Ivan-Lopez/Mano-Robotica/Images/others/dedoV2.jpg

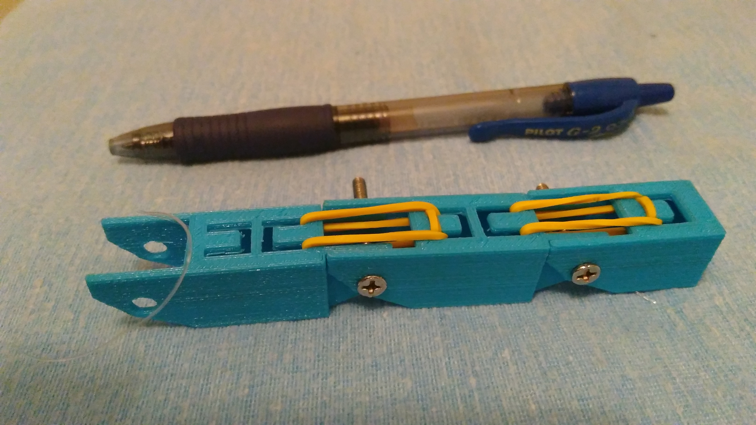
Images/others/dedoV2.jpg
