Ivan-Lopez/Mano-Robotica/Images/others/IMG_20180927_234917.jpg

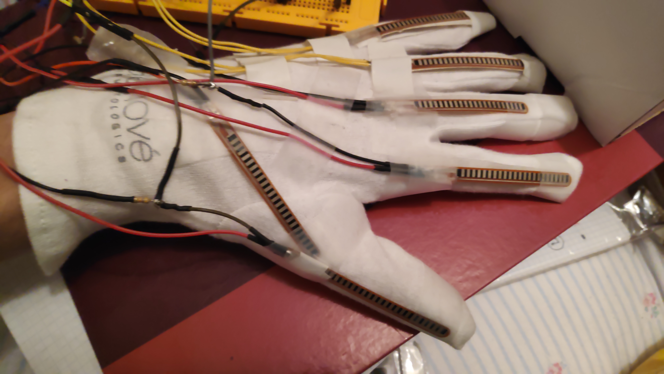
Images/others/IMG_20180927_234917.jpg
