Ivan-Lopez/Mano-Robotica/Images/plans/Falange distal meñique.jpg

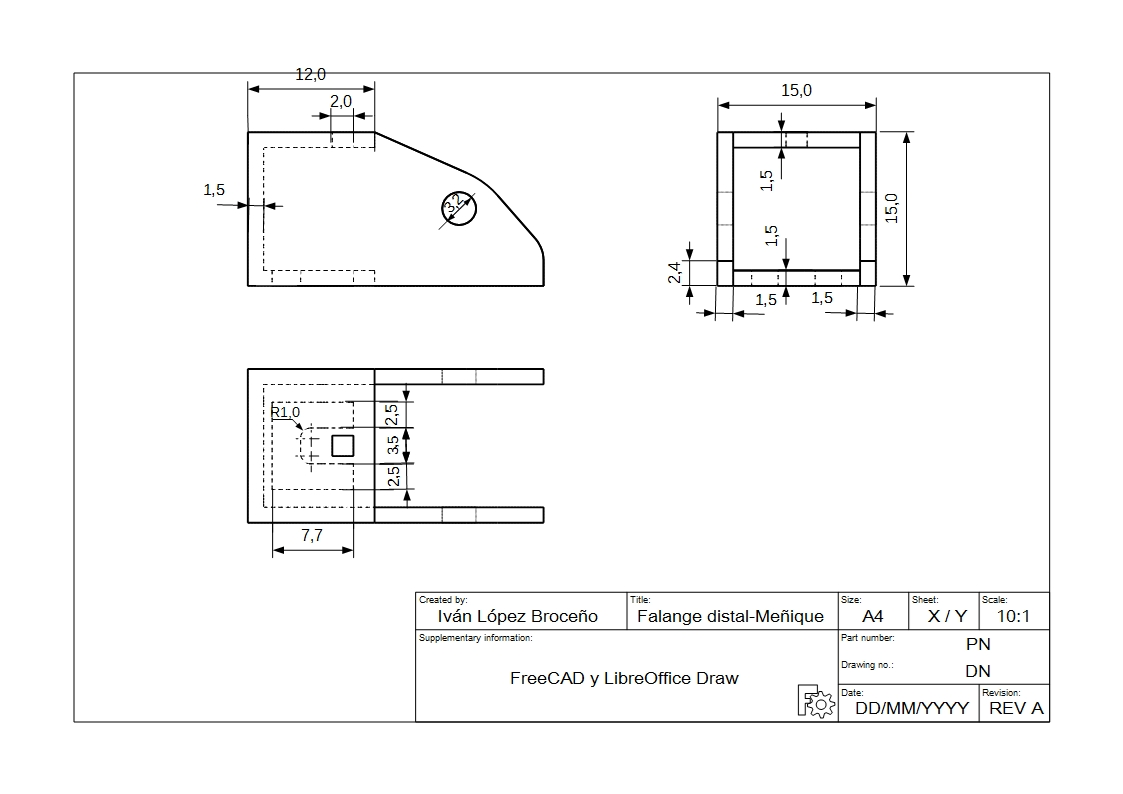
Images/plans/Falange distal meñique.jpg
