Ivan-Lopez/Mano-Robotica/Images/plans/falange distal pulgar.jpg

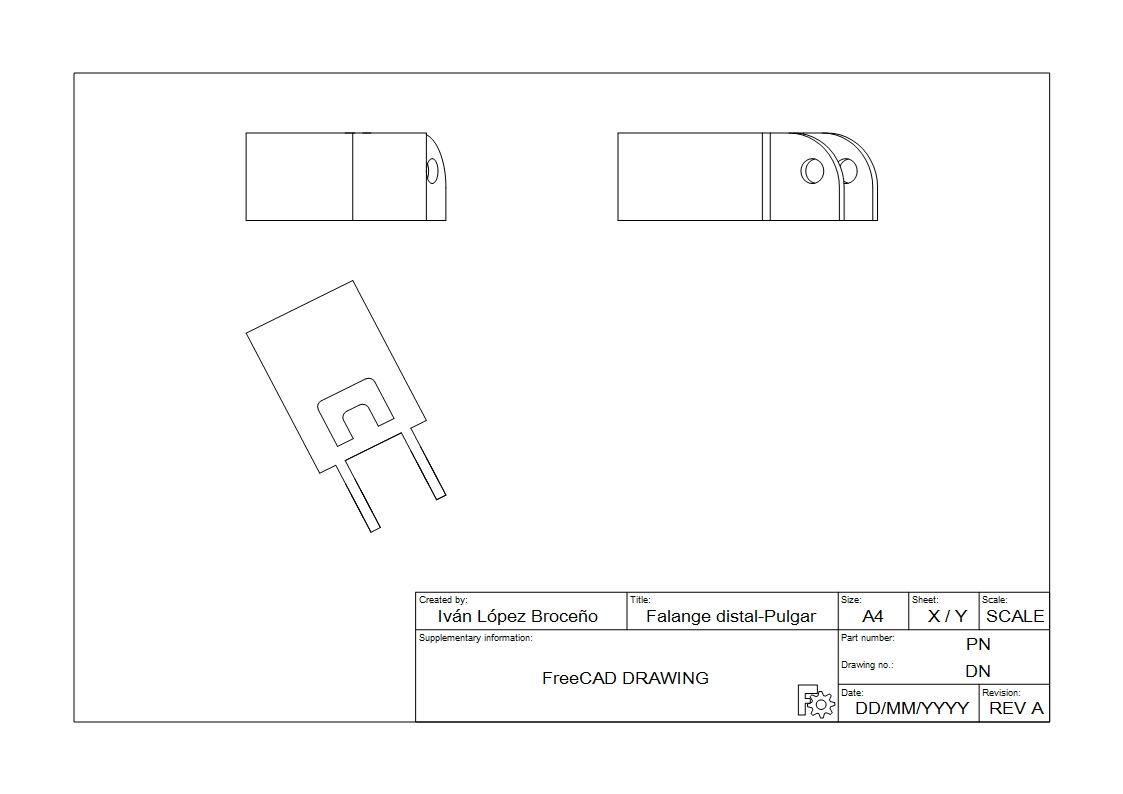
Images/plans/falange distal pulgar.jpg
