Ivan-Lopez/Mano-Robotica/Images/plans/parte inferior antebrazo.jpg

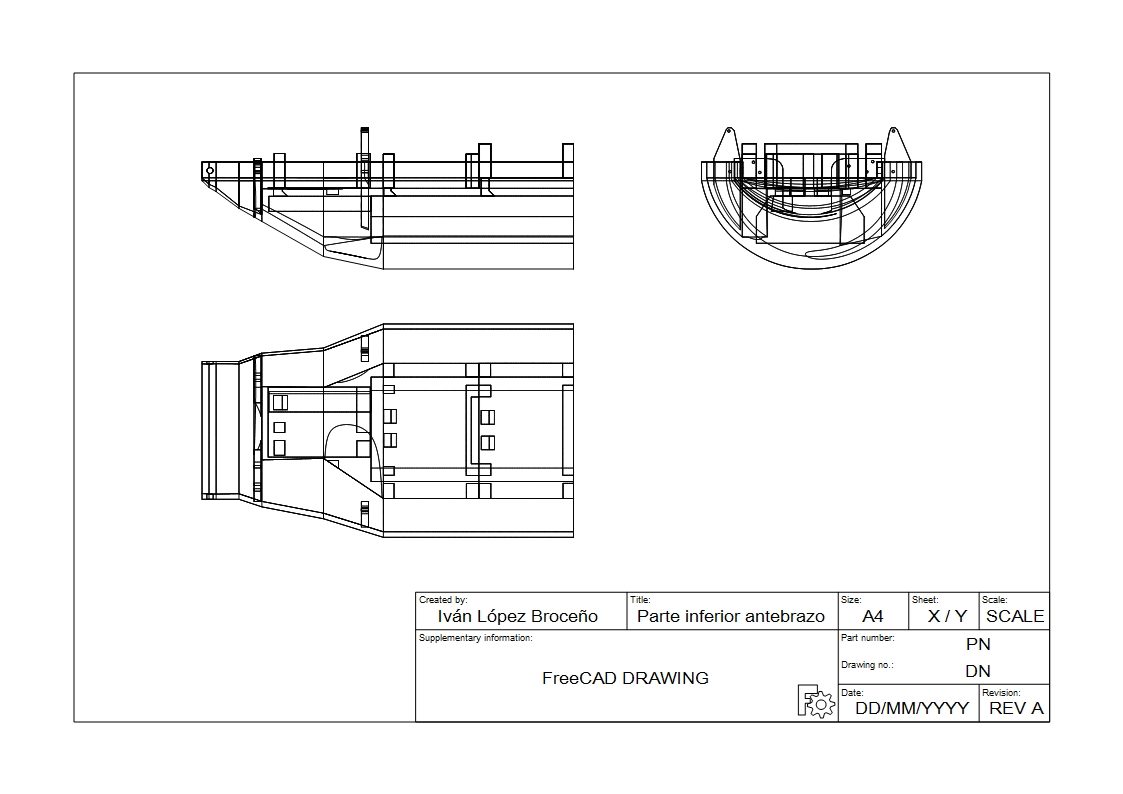
Images/plans/parte inferior antebrazo.jpg
