Ivan-Lopez/Mano-Robotica/Images/plans/Parte inferior de la palma.jpg

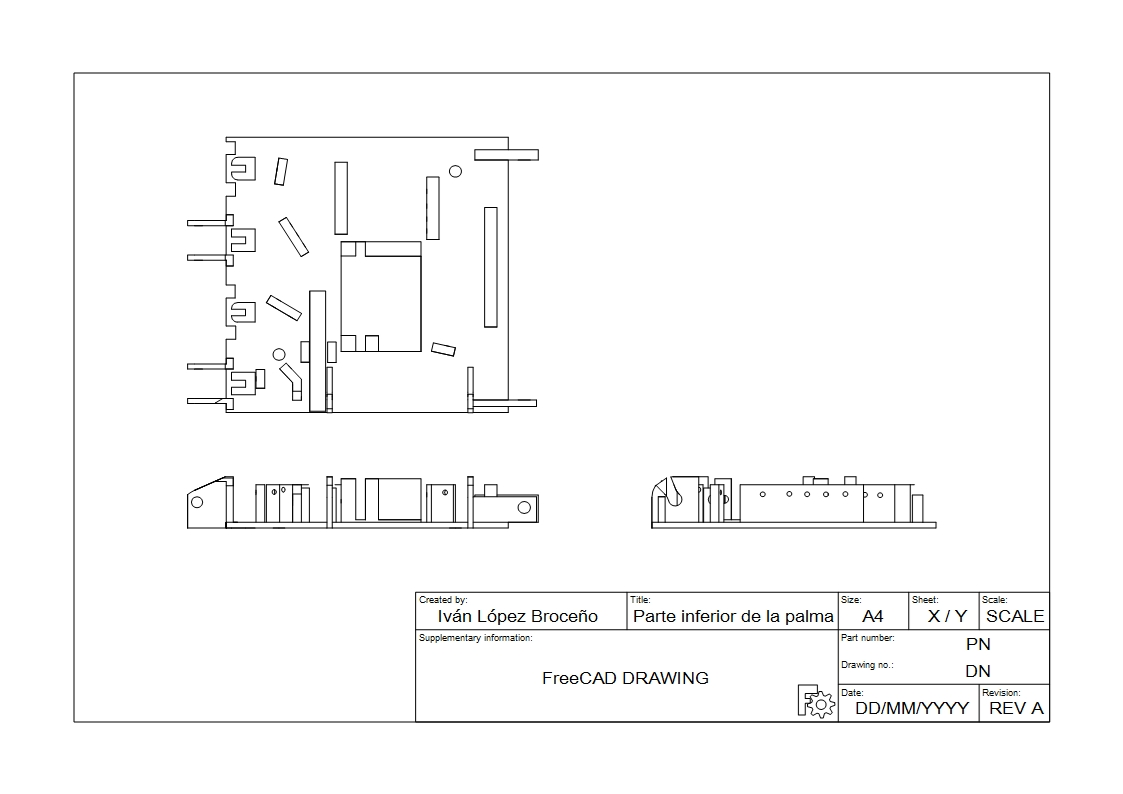
Images/plans/Parte inferior de la palma.jpg
