Ivan-Lopez/Mano-Robotica/Images/plans/parte superior antebrazo.jpg

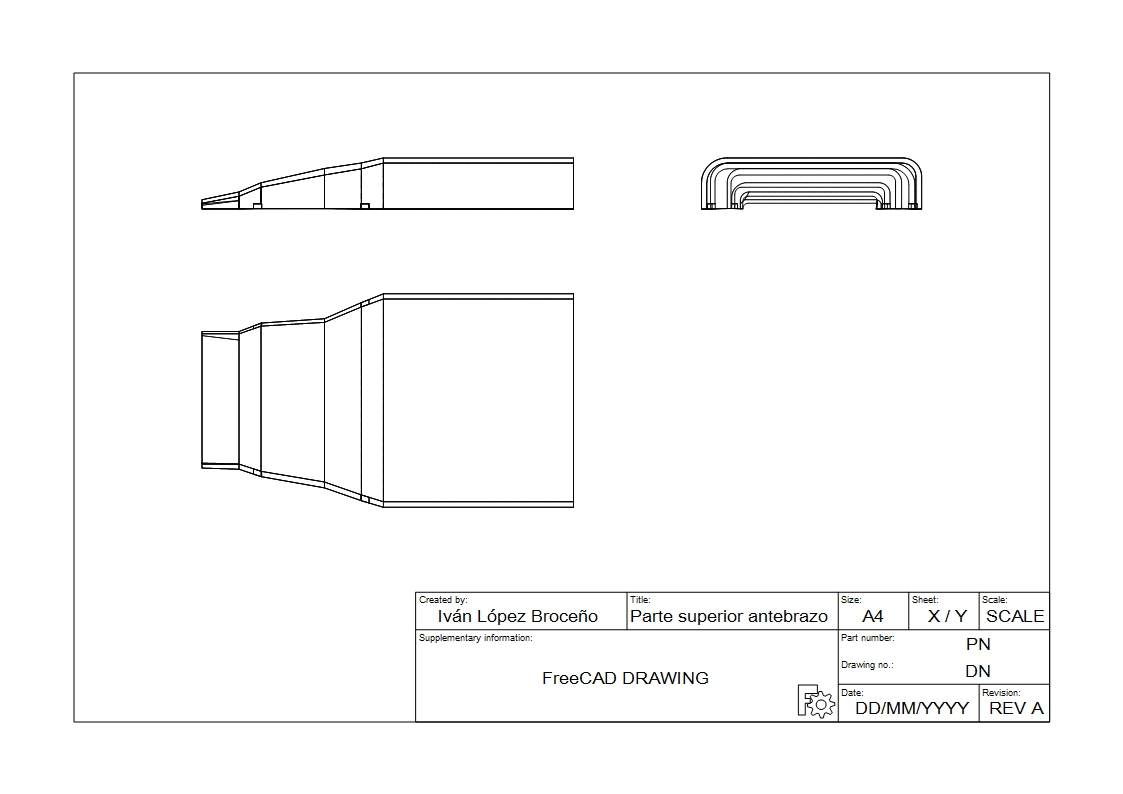
Images/plans/parte superior antebrazo.jpg
