Ivan-Lopez/Mano-Robotica/Images/plans/parte superior palma.jpg

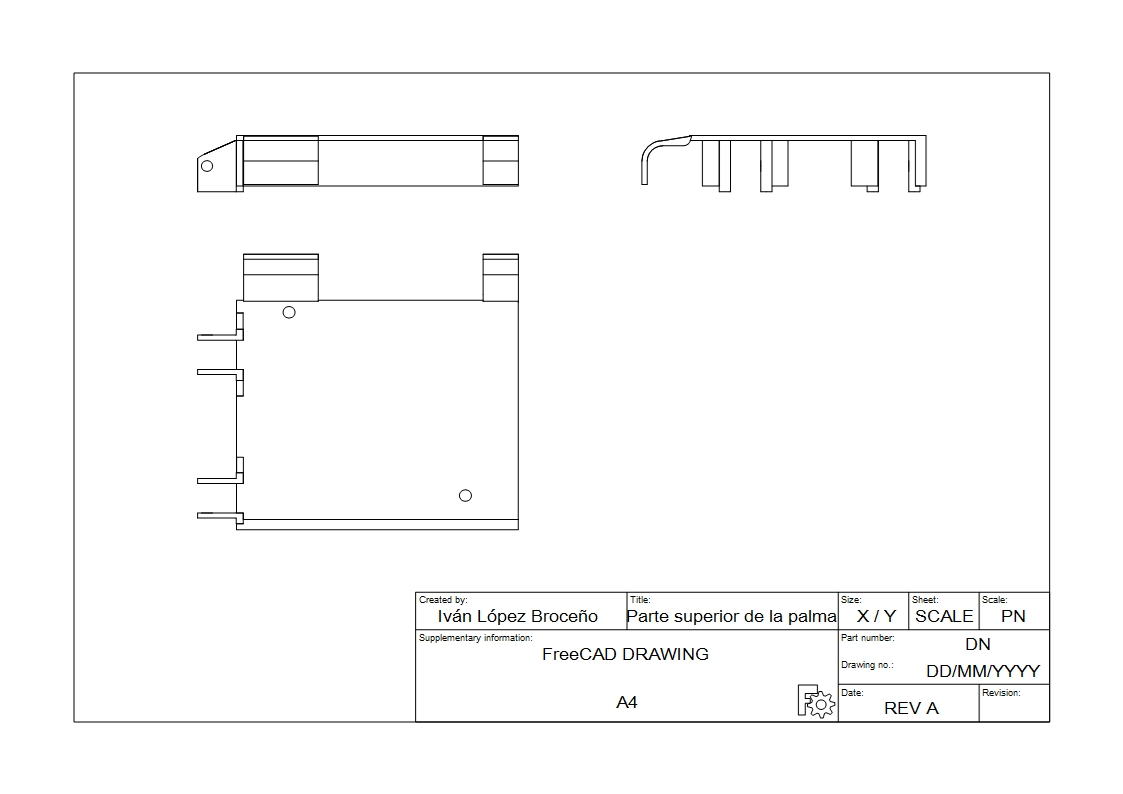
Images/plans/parte superior palma.jpg
