Ivan-Lopez/Mano-Robotica/Images/plans/Plano falange distal indiceVF2.jpg

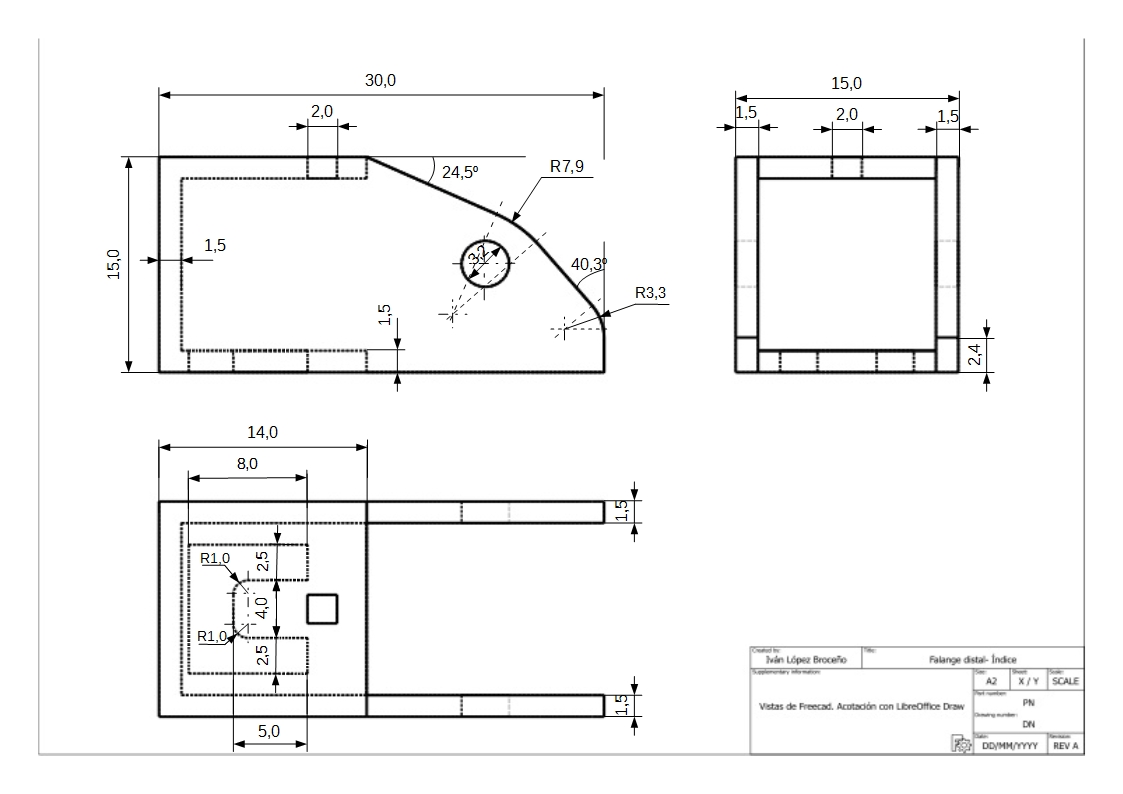
Images/plans/Plano falange distal indiceVF2.jpg
