Ivan-Lopez/Mano-Robotica/Images/plans/Plano falange medial y proximal-Índice.jpg

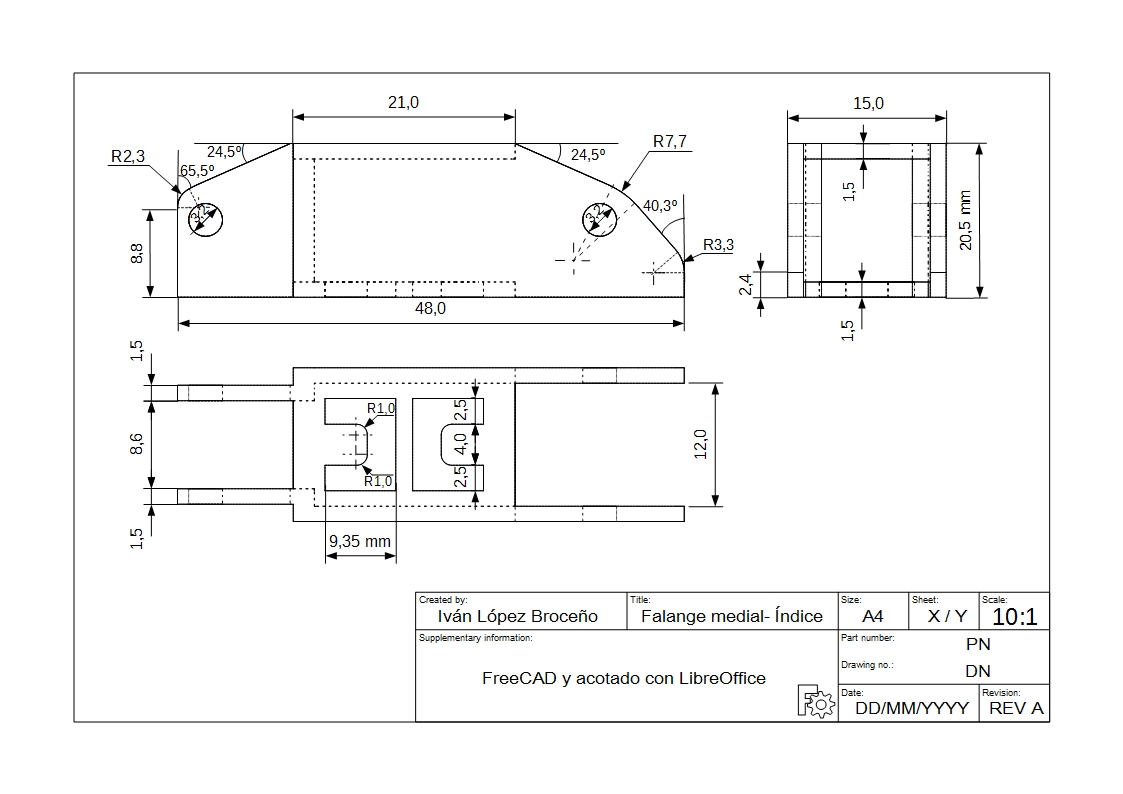
Images/plans/Plano falange medial y proximal-Índice.jpg
