Ivan-Lopez/Mano-Robotica/Images/plans/plano general descriptivo.png

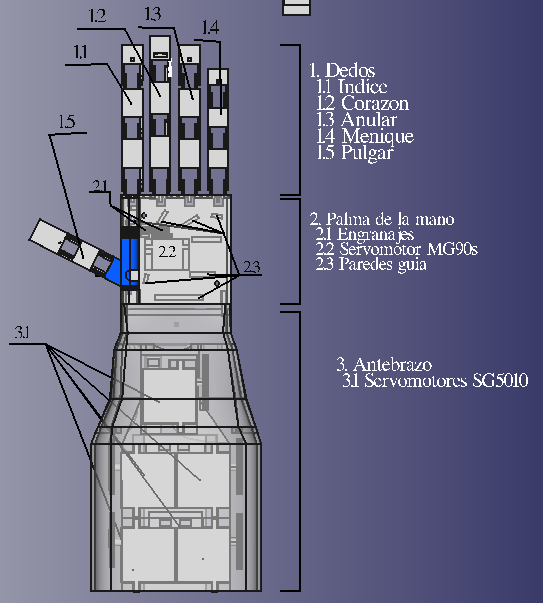
Images/plans/plano general descriptivo.png
