Ivan-Lopez/Mano-Robotica/Images/plans/union pulgar palam.jpg

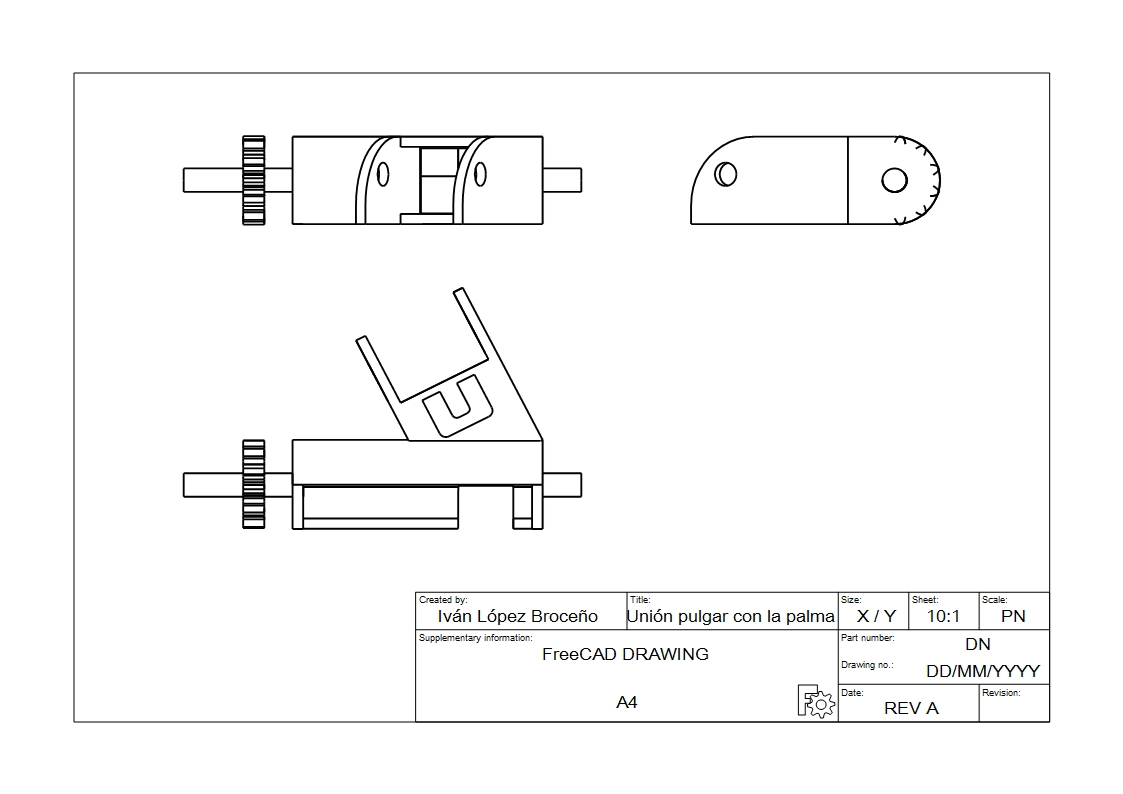
Images/plans/union pulgar palam.jpg
