Ivan-Lopez/Mano-Robotica/Images/schemes/esquema muscle sensor.png

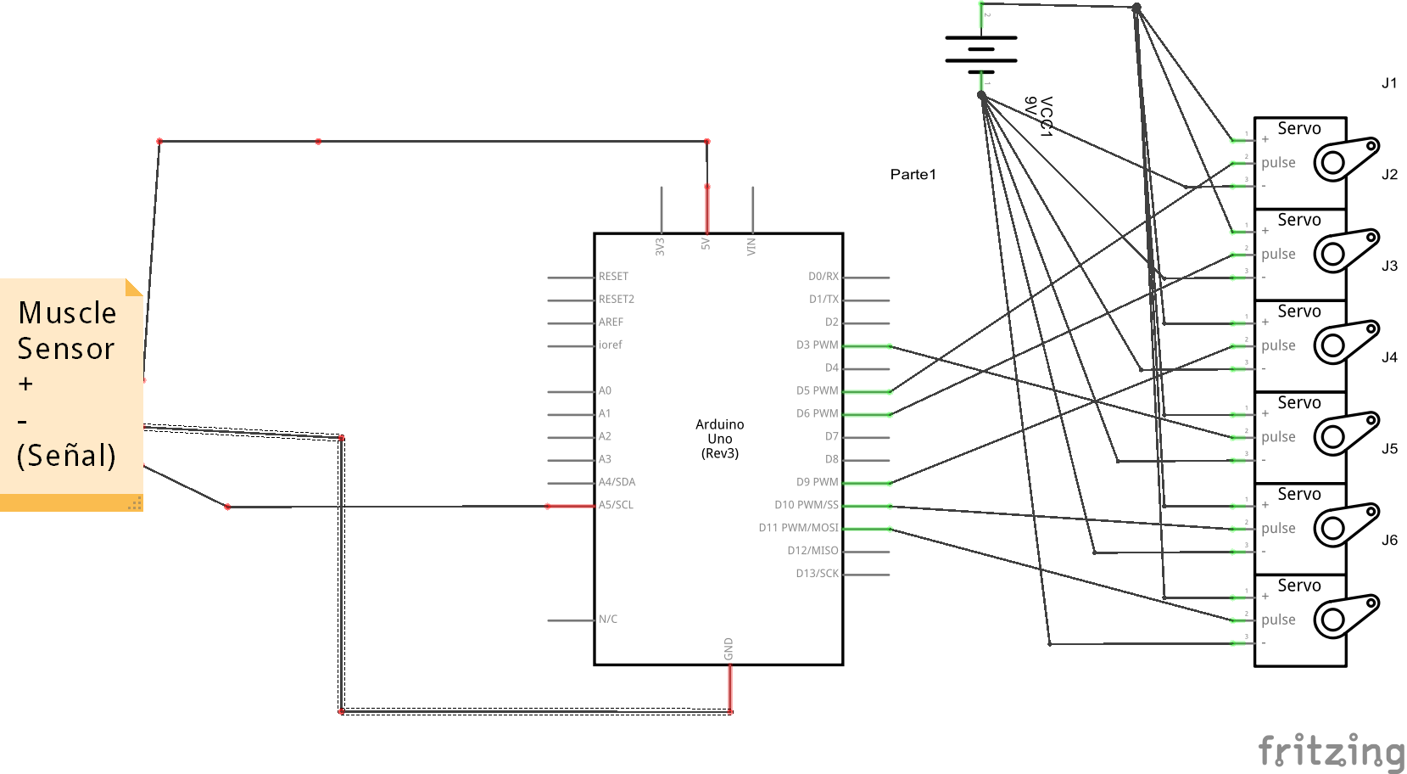
Images/schemes/esquema muscle sensor.png
