Ivan-Lopez/Mano-Robotica/Images/schemes/Esquema total, sensores flex.png

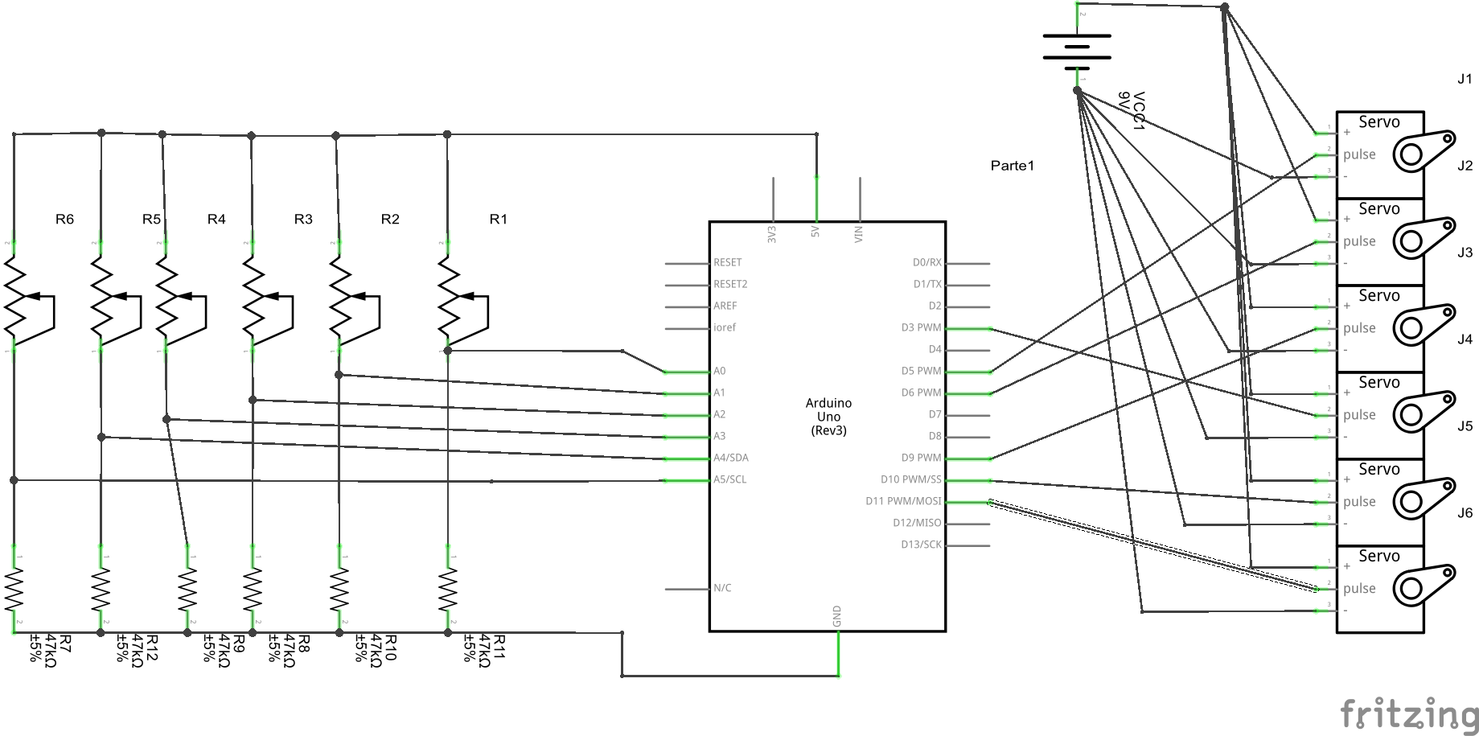
Images/schemes/Esquema total, sensores flex.png
