Ivan-Lopez/Mano-Robotica/Images/mass-time-cost table/Tabla Peso-Tiempo-Coste.jpg

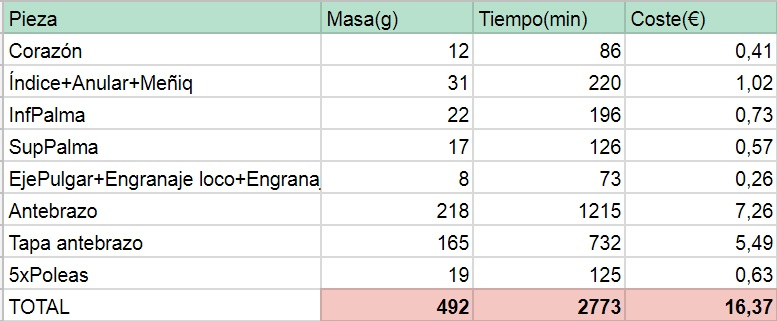
Images/mass-time-cost table/Tabla Peso-Tiempo-Coste.jpg
