Ivan-Lopez/Mano-Robotica/Diseños-Designs/Dedos-Fingers/Pulgar-Thumb/falange2-pulgar.stl

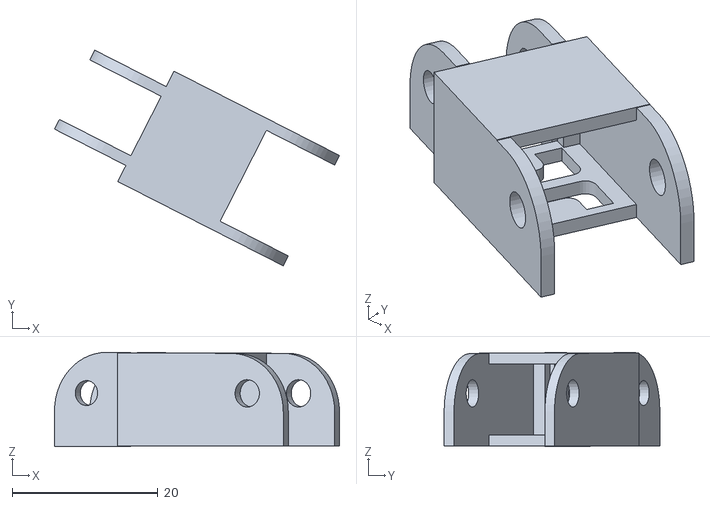
[picture p35: CAD file, 2019-02-16]
Diseños-Designs/Dedos-Fingers/Pulgar-Thumb/falange2-pulgar.stl
39.1 x 29.6 x 12.9
