Ivan-Lopez/Mano-Robotica/Diseños-Designs/Dedos-Fingers/Índice-Index Finger/falange3-indiceV2.stl

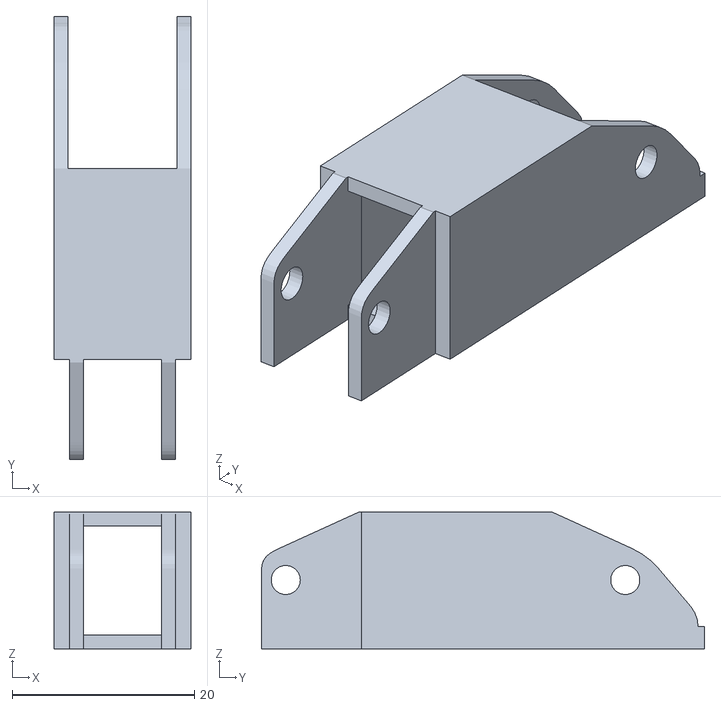
[picture p36: CAD file, 2019-02-16]
Diseños-Designs/Dedos-Fingers/Índice-Index Finger/falange3-indiceV2.stl
15.0 x 48.7 x 15.0
