Ivan-Lopez/Mano-Robotica/Diseños-Designs/Dedos-Fingers/Corazón-Middle Finger/falange3-corazonV2.stl

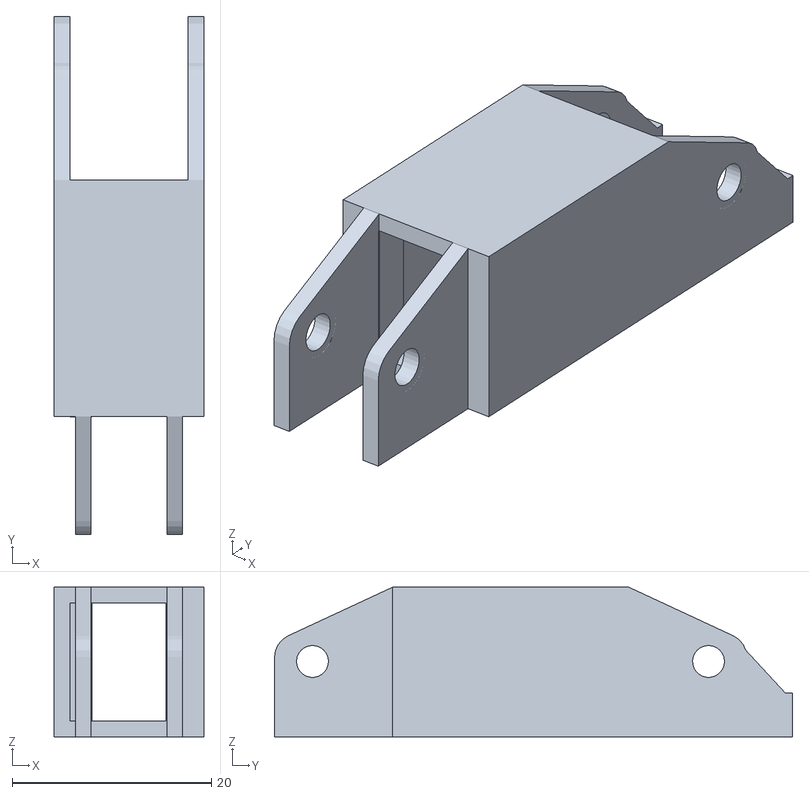
[picture p37: CAD file, 2019-02-16]
Diseños-Designs/Dedos-Fingers/Corazón-Middle Finger/falange3-corazonV2.stl
15.0 x 51.9 x 15.0
